skot/bitaxeHex/Web-Bench/WBDesign-5V.pdf

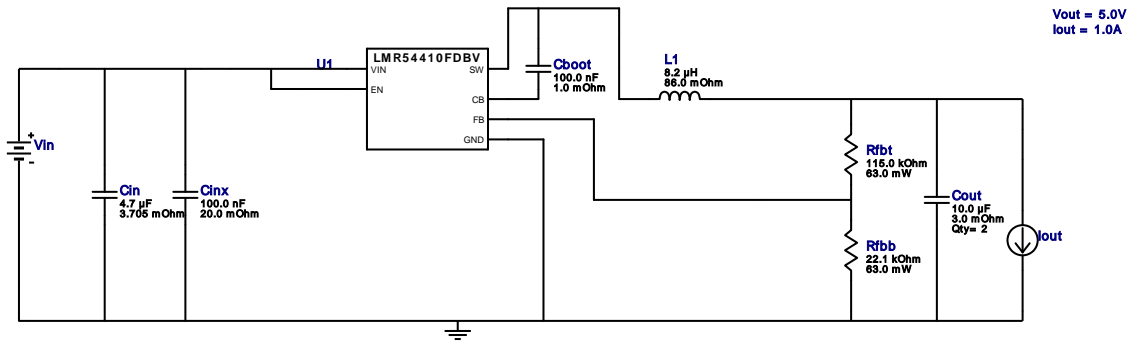
[picture p21: figure]
LM R5 4 4 1 0 FDBV; GND; VIN; Cout 10.0 µF 3.0 m Ohm Qty= 2; Cinx 100.0 nF 20.0 m Ohm; L1 8.2 µH 86.0 m Ohm; Rfbb 22.1 kOhm 63.0 m W; Rfbt 115.0 kOhm 63.0 m W; Vout = 5.0V Iout = 1.0A; Cboot 100.0 nF 1.0 m Ohm; Cin 4.7 µF 3.705 m Ohm; Vin; Iout

Copyright © 2023, Texas Instruments Incorporated | 1 | ti.com/webench

WEBENCH®
Design Report LMR54410FDBVR : LMR54410FDBVR 11V-16V to 5.00V @ 1A December 9, 2023 01:14:49 GMT-06:00

## WEBENCH ® Design Report

Design : 11 LMR54410FDBVR
LMR54410FDBVR 11V-16V to 5.00V @ 1A

VinMin = 11.0V
VinMax = 16.0V
Vout = 5.0V
Iout = 1.0A

Device = LMR54410FDBVR
Topology = Buck
Created = 2023-12-08 23:25:29.060 BOM Cost = $1.70
BOM Count = 9
Total Pd = 0.55W

## Electrical BOM

Name | Manufacturer | Part Number | Properties | Qty Price | Footprint
Cboot | MuRata | GRM155R71C104KA88D (http://search.murata.co.jp/Ceramy/PnsearchViewAction.do) Series= X7R | Cap= 100.0 nF ESR= 1.0 mOhm VDC= 16.0 V IRMS= 0.0 A
1 | $0.01
| | | | | 0402 3 mm²
Cin | MuRata | GRM31CR71E475KA88L (http://psearch.en.murata.com/capacitor/result/smd/?status%3Dall%26pid%3DGRM31CR71E475KA88L) Series= X7R

Cap= 4.7 uF
ESR= 3.705 mOhm
VDC= 25.0 V
IRMS= 2.8649 A

1 $0.09
1206_190 11 mm²
Cinx | MuRata | GRM188R71H104KA93D Series= X7R

Cap= 100.0 nF
ESR= 20.0 mOhm
VDC= 50.0 V
IRMS= 3.8 A

1 $0.02
0603 5 mm²
Cout | Kemet | C0805C106K8PACTU (http://capacitoredge.kemet.com/capedge2/DataSheet/Datasheet%2DC0805C106K8PACTU.pdf?pn%3DC0805C106K8PACTU) Series= X5R

Cap= 10.0 uF
ESR= 3.0 mOhm
VDC= 10.0 V
IRMS= 11.43 A

2 $0.03
0805 7 mm²
L1 | Wurth Elektronik | 74438357082 (http://katalog.we%2Donline.de/pbs/datasheet/74438357082.pdf) | L= 8.2 µH 86.0 mOhm | 1 | $1.22
WE-MAPI_4030 26 mm²
Rfbb | Vishay-Dale | CRCW040222K1FKED (http://www.vishay.com/docs/20035/dcrcwe3.pdf) Series= CRCW..e3 | Res= 22.1 kOhm Power= 63.0 mW Tolerance= 1.0% | 1 | $0.01
0402 3 mm²
Rfbt | Vishay-Dale | CRCW0402115KFKED (http://www.vishay.com/docs/20035/dcrcwe3.pdf) Series= CRCW..e3 | Res= 115.0 kOhm Power= 63.0 mW Tolerance= 1.0% | 1 | $0.01
0402 3 mm²
U1 | Texas Instruments | LMR54410FDBVR (http://www.ti.com/product/LMR54410) | Switcher | 1 | $0.28

DBV0006A 15 mm²

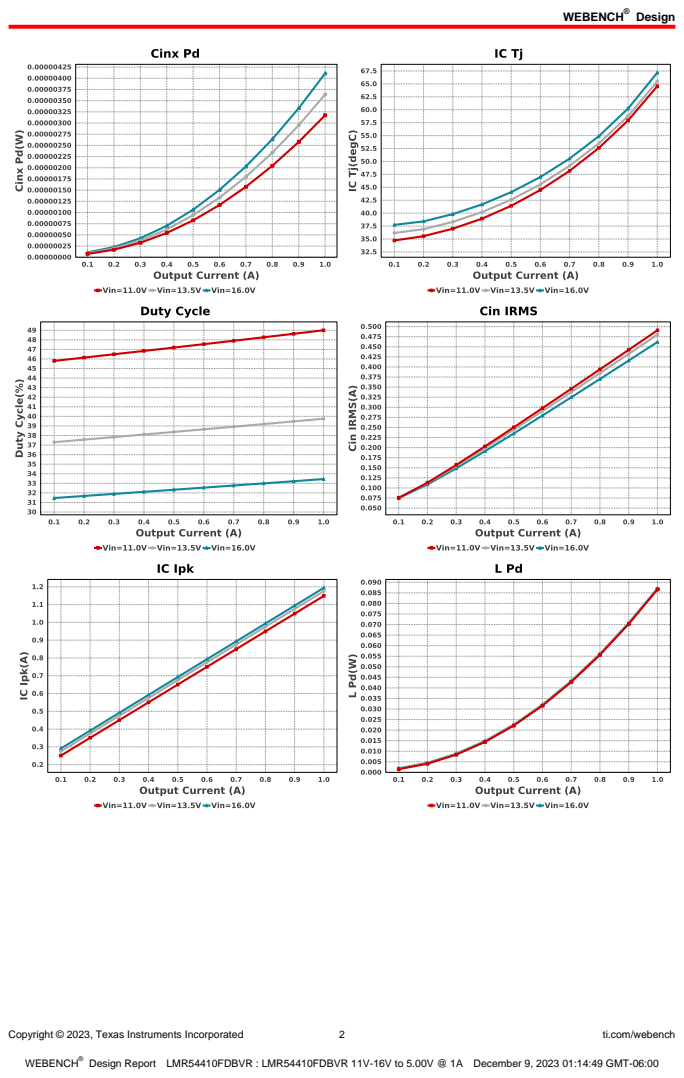
[picture p22: page 2]
Design; Copyright © 2023, Texas Instruments Incorporated; ti.com/webench

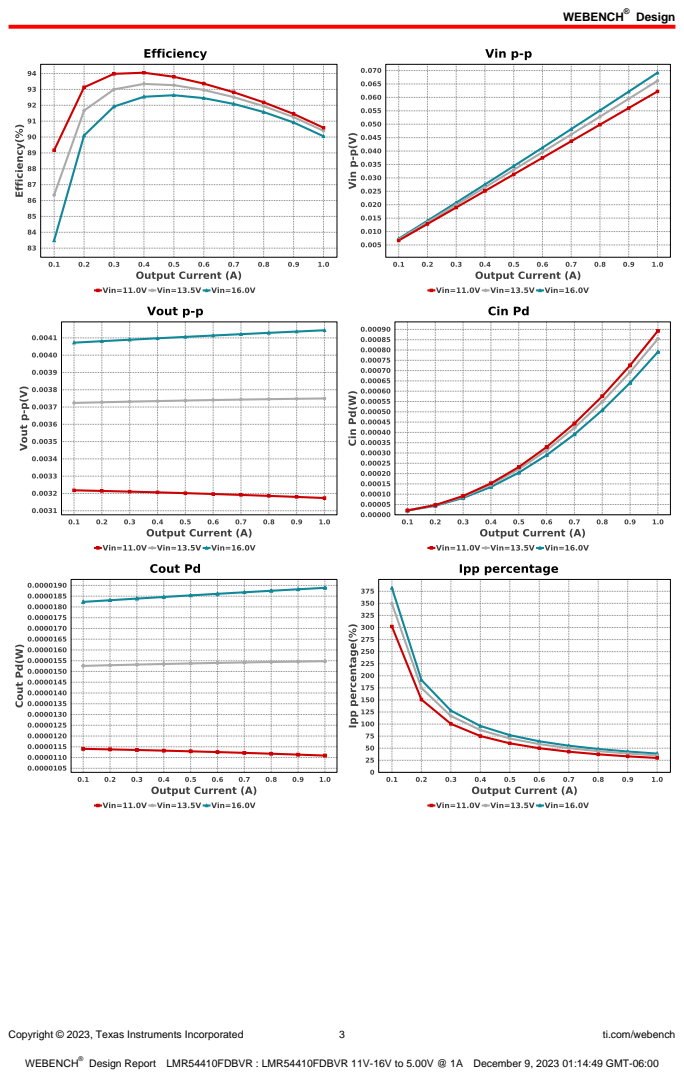
[picture p23: page 3]
Copyright © 2023, Texas Instruments Incorporated; ti.com/webench

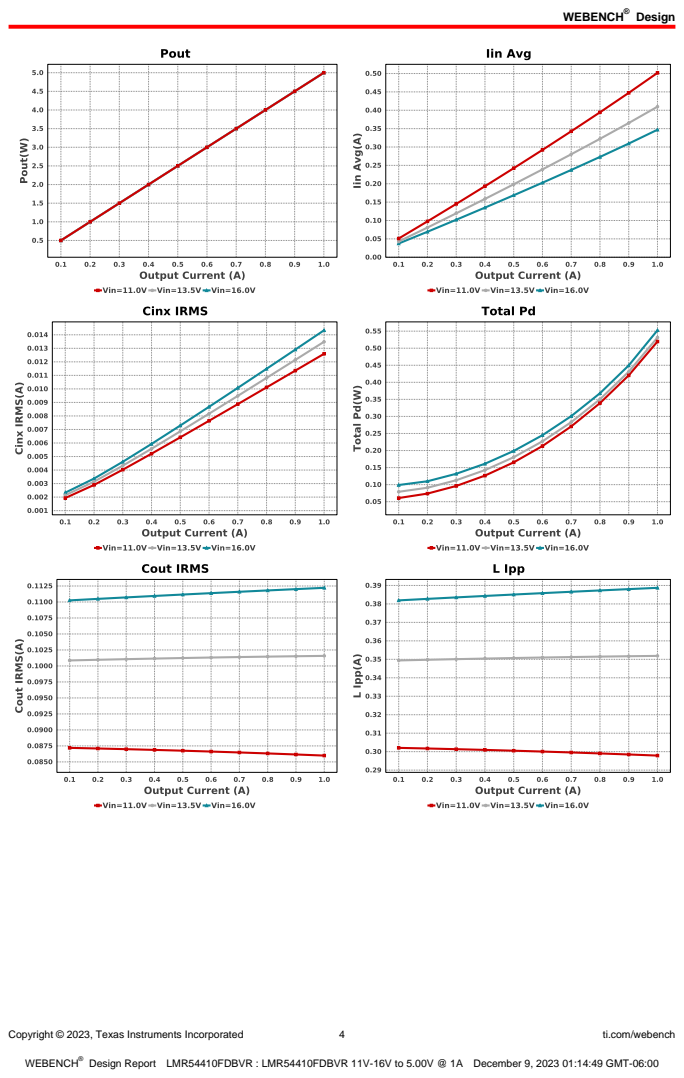
[picture p24: page 4]
Copyright © 2023, Texas Instruments Incorporated; ti.com/webench

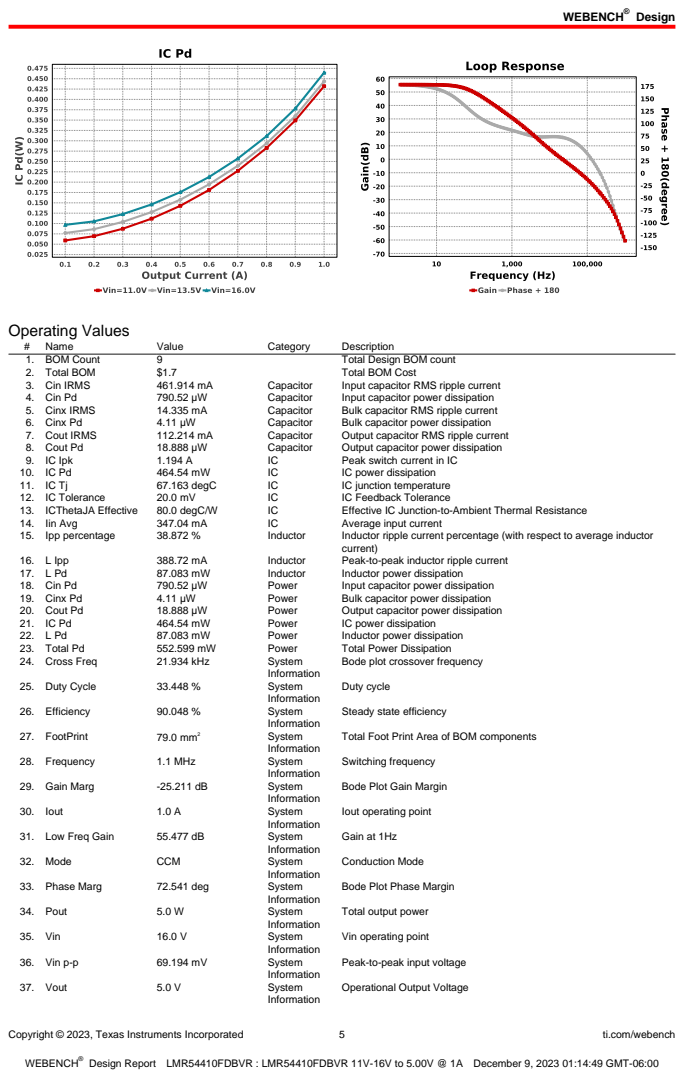
[picture p25: page 5]
Copyright © 2023, Texas Instruments Incorporated; ti.com/webench; Operating Values; Name; Value; Category; Description; 1. BOM Count; Total Design BOM count; 2. Total BOM; Total BOM Cost; 3. Cin IRMS; Capacitor; Input capacitor RMS ripple current; 4. Cin Pd; Input capacitor power dissipation; 5. Cinx IRMS; Bulk capacitor RMS ripple current; 6. Cinx Pd; Bulk capacitor power dissipation; 7. Cout IRMS; Output capacitor RMS ripple current; 8. Cout Pd; Output capacitor power dissipation; 9. IC Ipk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

Bode plot crossover frequency

Steady state efficiency

Total Foot Print Area of BOM components

Bode Plot Gain Margin

Iout operating point

Bode Plot Phase Margin

Total output power

Vin operating point

Peak-to-peak input voltage

Operational Output Voltage

Copyright © 2023, Texas Instruments Incorporated | 6 | ti.com/webench
# | Name | Value | Category | Description

38. Vout Actual | 4.963 V | System
| | | Information | Vout Actual calculated based on selected voltage divider resistors
39. Vout Tolerance | 4.237 % | System
| | | Information | Vout Tolerance based on IC Tolerance (no load) and voltage divider resistors if applicable
40. Vout p-p | 4.144 mV | System
| | | Information | Peak-to-peak output ripple voltage

## Design Inputs

Name | Value | Description
Iout | 1.0 | Maximum Output Current
VinMax | 16.0 | Maximum input voltage
VinMin | 11.0 | Minimum input voltage
Vout | 5.0 | Output Voltage
| base_pn | | LMR54410F | Base Product Number
source | DC | Input Source Type
Ta | 30.0 | Ambient temperature


Copyright © 2023, Texas Instruments Incorporated | 7 | ti.com/webench

## Assembly

## Component Testing

Some published data on components in datasheets such as Capacitor ESR and Inductor DC resistance is based on conservative values that will guarantee that the components always exceed the specification. For design purposes it is usually better to work with typical values. Since this data is not always available it is a good practice to measure the Capacitance and ESR values of Cin and Cout, and the inductance and DC resistance of L1 before assembly of the board. Any large discrepancies in values should be electrically simulated in WEBENCH to check for instabilities and thermally simulated in WebTHERM to make sure critical temperatures are not exceeded.

## Soldering Component to Board

If board assembly is done in house it is best to tack down one terminal of a component on the board then solder the other terminal. For surface mount parts with large tabs, such as the DPAK, the tab on the back of the package should be pre-tinned with solder, then tacked into place by one of the pins. To solder the tab town to the board place the iron down on the board while resting against the tab, heating both surfaces simultaneously. Apply light pressure to the top of the plastic case until the solder flows around the part and the part is flush with the PCB. If the solder is not flowing around the board you may need a higher wattage iron (generally 25W to 30W is enough).

## Initial Startup of Circuit

It is best to initially power up the board by setting the input supply voltage to the lowest operating input voltage 11.0V and set the input supply's current limit to zero. With the input supply off connect up the input supply to Vin and GND. Connect a digital volt meter and a load if needed to set the minimum Iout of the design from Vout and GND. Turn on the input supply and slowly turn up the current limit on the input supply.
If the voltage starts to rise on the input supply continue increasing the input supply current limit while watching the output voltage. If the current increases on the input supply, but the voltage remains near zero, then there may be a short or a component misplaced on the board. Power down the board and visually inspect for solder bridges and recheck the diode and capacitor polarities. Once the power supply circuit is operational then more extensive testing may include full load testing, transient load and line tests to compare with simulation results.

## Load Testing

The setup is the same as the initial startup, except that an additional digital voltmeter is connected between Vin and GND, a load is connected between Vout and GND and a current meter is connected in series between Vout and the load. The load must be able to handle at least rated output power + 50% ( 7.5 watts for this design). Ideally the load is supplied in the form of a variable load test unit. It can also be done in the form of suitably large power resistors. When using an oscilloscope to measure waveforms on the prototype board, the ground leads of the oscilloscope probes should be as short as possible and the area of the loop formed by the ground lead should be kept to a minimum. This will help reduce ground lead inductance and eliminate EMI noise that is not actually present in the circuit.

## Design Assistance

1. Master key : 330B248541F6394ED110965082F3CA95[v1]
2. LMR54410F Product Folder : http://www.ti.com/product/LMR54410 : contains the data sheet and other resources.

Copyright © 2023, Texas Instruments Incorporated | 8 | ti.com/webench

Important Notice and Disclaimer

TI provides technical and reliability data (including datasheets), design resources (including reference designs), application or other design advice, web tools, safety information, and other resources AS IS and with all faults, and disclaims all warranties. These resources are intended for skilled developers designing with TI products. You are solely responsible for (1) selecting the appropriate TI products for your application, (2) designing, validating and testing your application, and (3) ensuring your application meets applicable standards, and any other safety, security, or other requirements.

These resources are subject to change without notice. TI grants you permission to use these resources only for development of an application that uses the TI products described in the resource. Other reproduction and display of these resources is prohibited. No license is granted to any other TI intellectual property right or to any third party intellectual property right. TI disclaims responsibility for, and you will fully indemnify TI and its representatives against, any claims, damages, costs, losses, and liabilities arising out of your use of these resources.

Providing these resources does not expand or otherwise alter TI's applicable Terms of Sale or other applicable terms available either on ti.com or provided in conjunction with TI products.
